redstonee/XClock/resource/Overview/IMG_20241222_154358.jpg

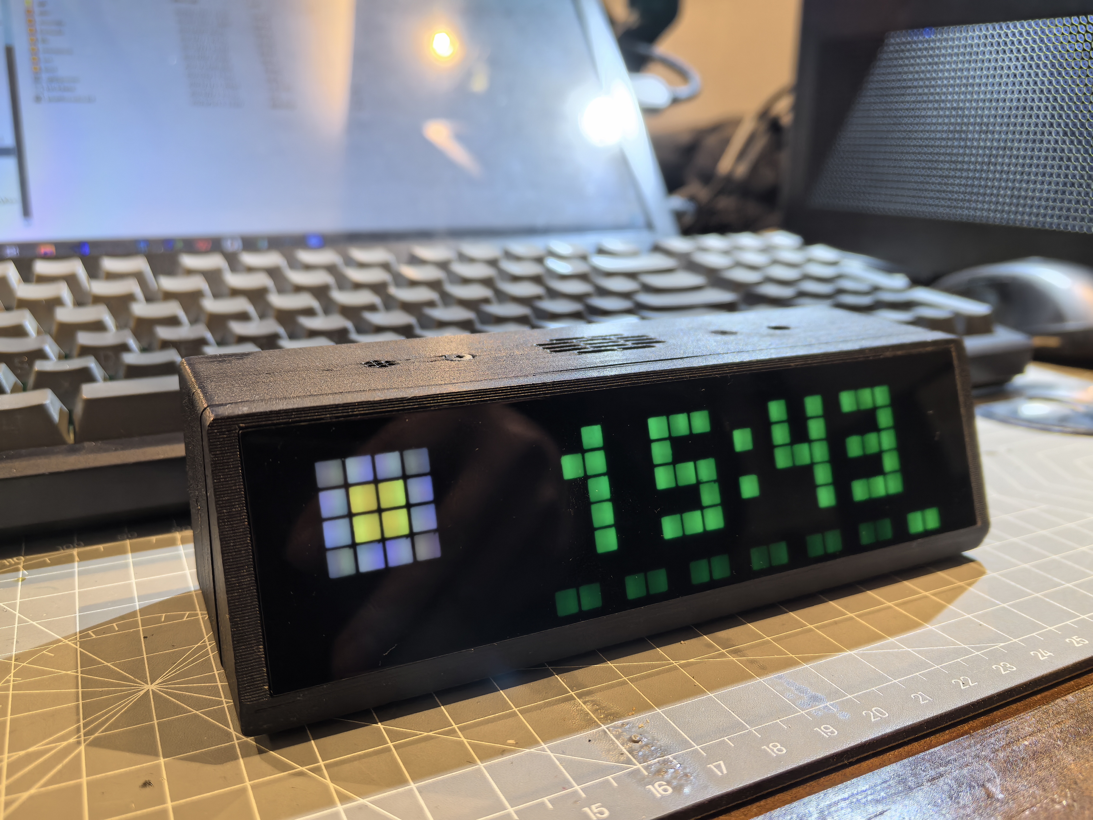
resource/Overview/IMG_20241222_154358.jpg
