redstonee/XClock/resource/Overview/IMG_20241222_154428.jpg

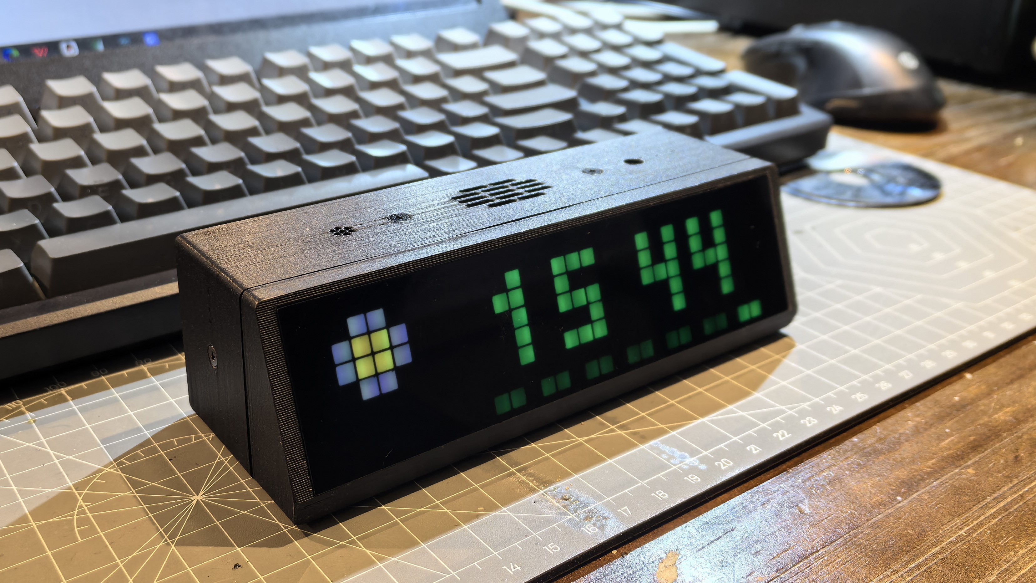
resource/Overview/IMG_20241222_154428.jpg
