redstonee/XClock/resource/Overview/IMG_20241222_154616.jpg

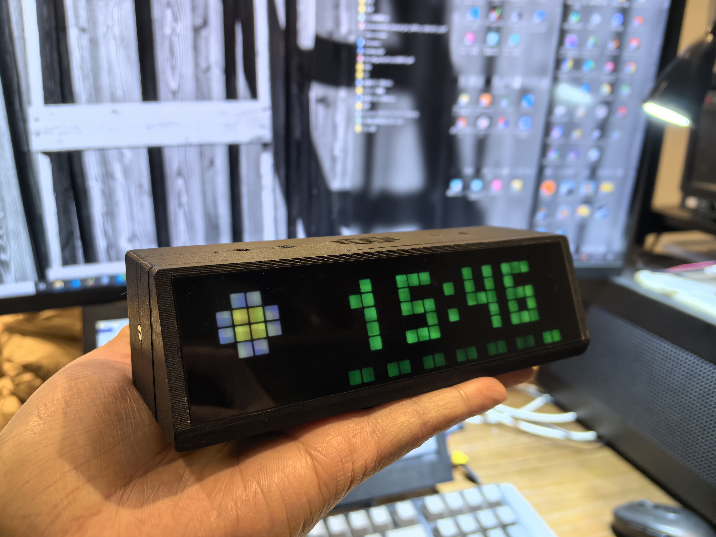
resource/Overview/IMG_20241222_154616.jpg
