redstonee/XClock/resource/Overview/IMG_20241222_154702.jpg

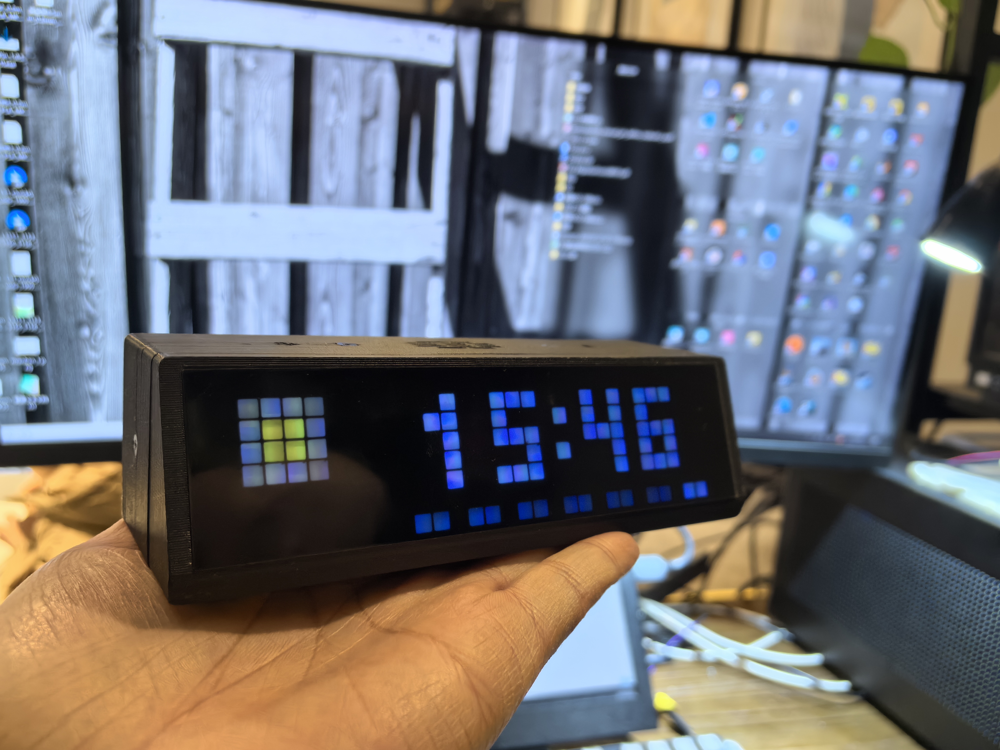
resource/Overview/IMG_20241222_154702.jpg
