redstonee/XClock/resource/Overview/IMG_20241222_154757.jpg

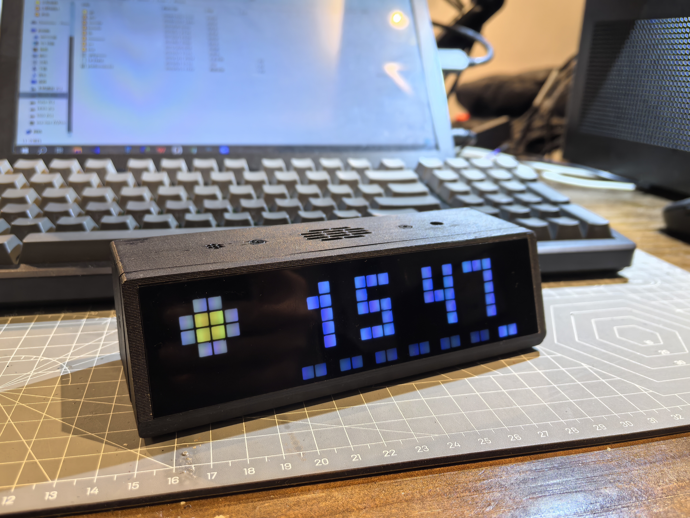
resource/Overview/IMG_20241222_154757.jpg
