redstonee/XClock/resource/Overview/IMG_20241222_154823.jpg

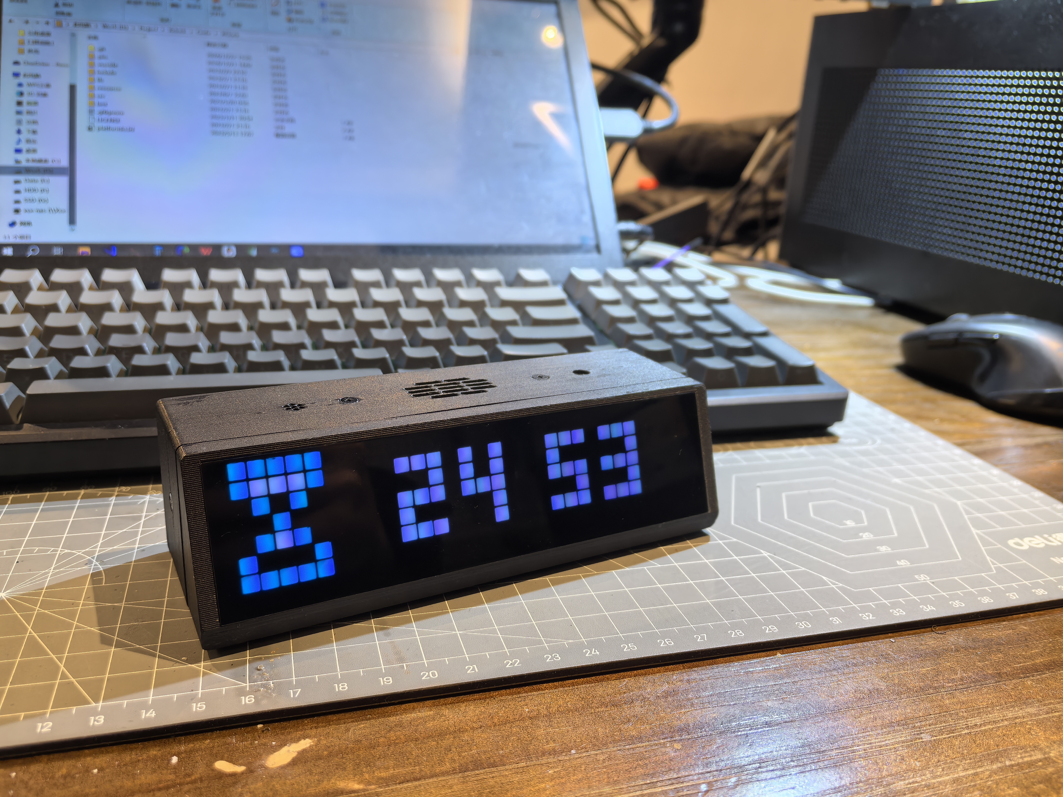
resource/Overview/IMG_20241222_154823.jpg
