redstonee/XClock/resource/Overview/IMG_20241222_154830.jpg

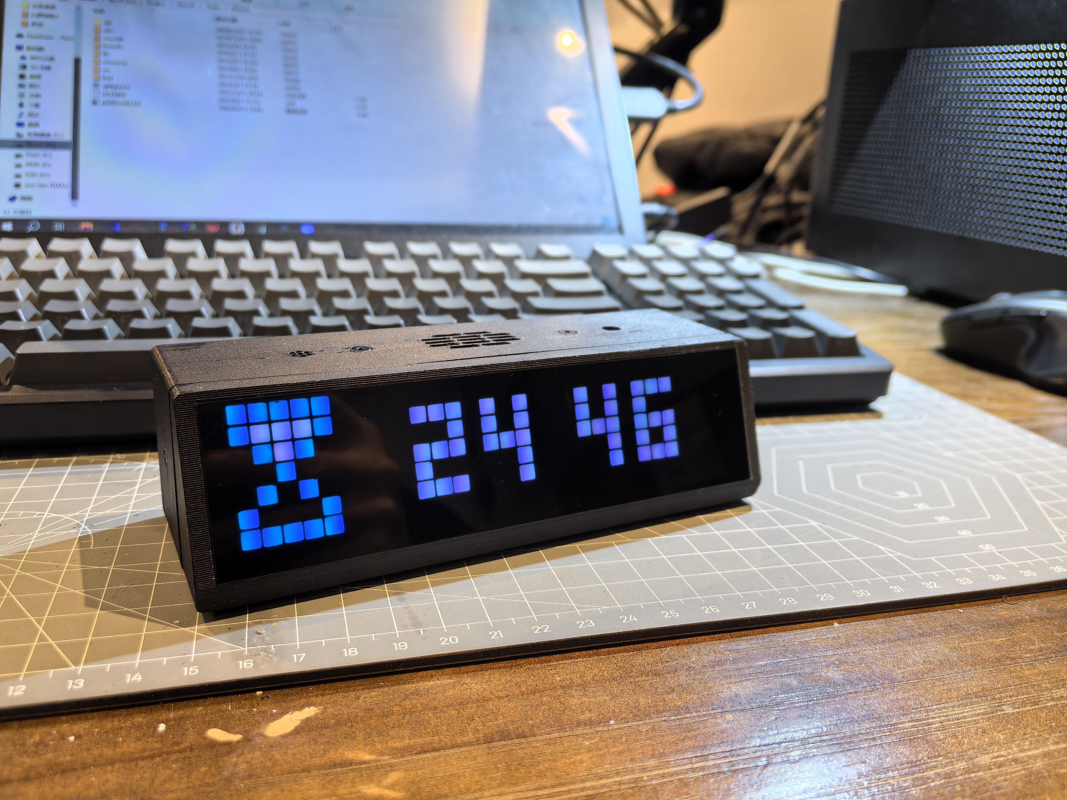
resource/Overview/IMG_20241222_154830.jpg
