redstonee/XClock/resource/Overview/IMG_20241222_155135.jpg

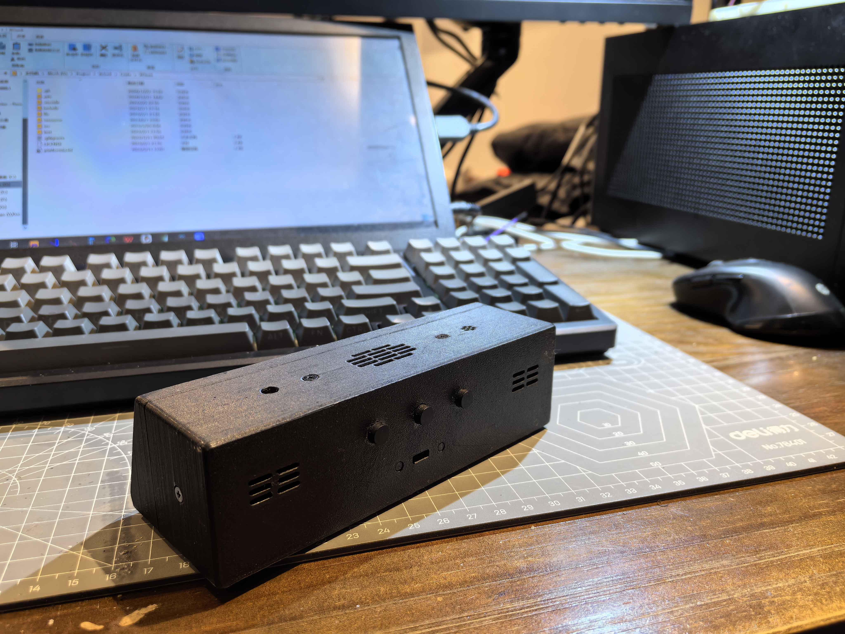
resource/Overview/IMG_20241222_155135.jpg
