redstonee/XClock/resource/Overview/IMG_20241222_163454.jpg

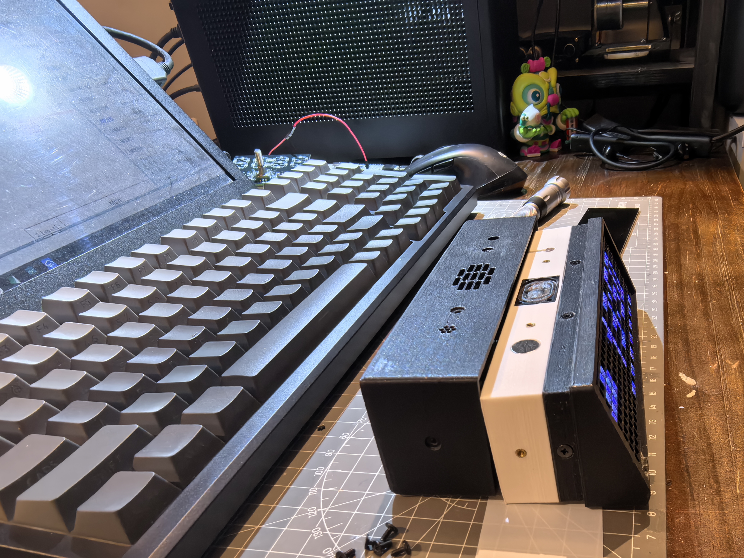
resource/Overview/IMG_20241222_163454.jpg
