redstonee/XClock/resource/Overview/IMG_20241222_1544281.jpg

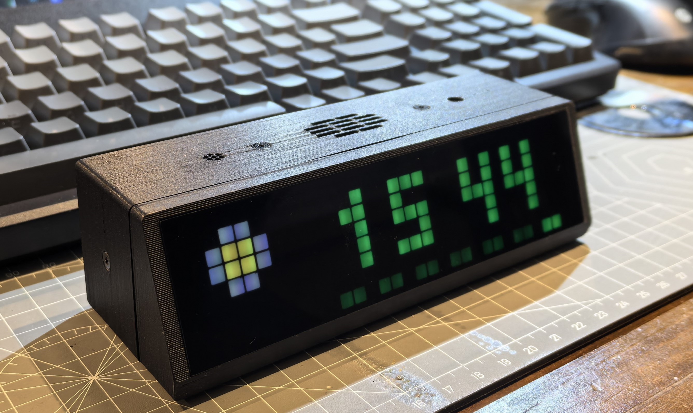
resource/Overview/IMG_20241222_1544281.jpg
