redstonee/XClock/resource/图标/GIF制作步骤/Pixilart画像素图片1.jpg

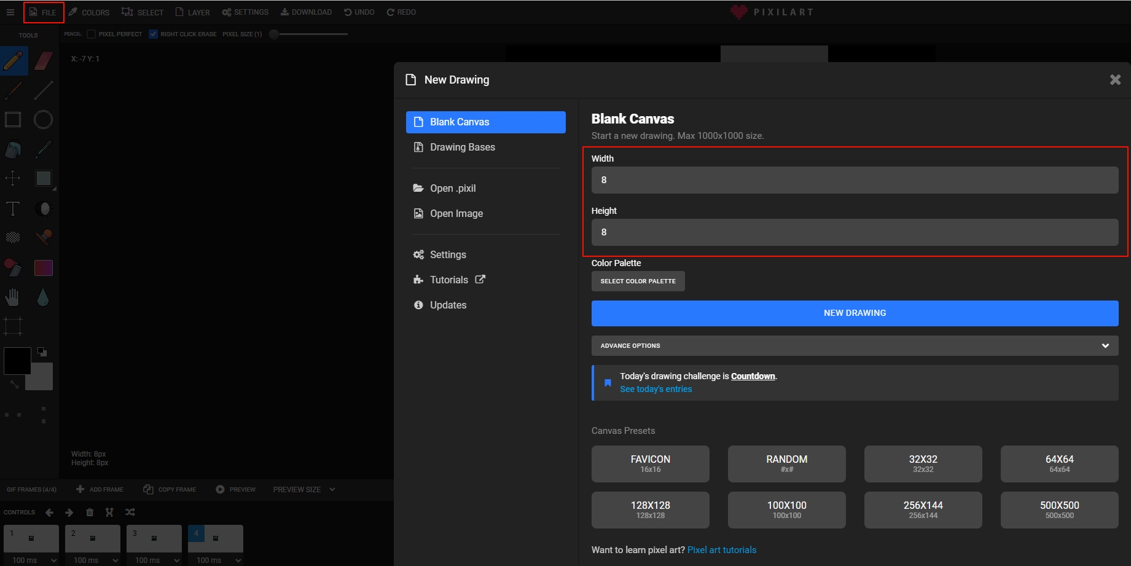
resource/图标/GIF制作步骤/Pixilart画像素图片1.jpg
