redstonee/XClock/resource/图标/GIF制作步骤/Pixilart画像素图片5.jpg

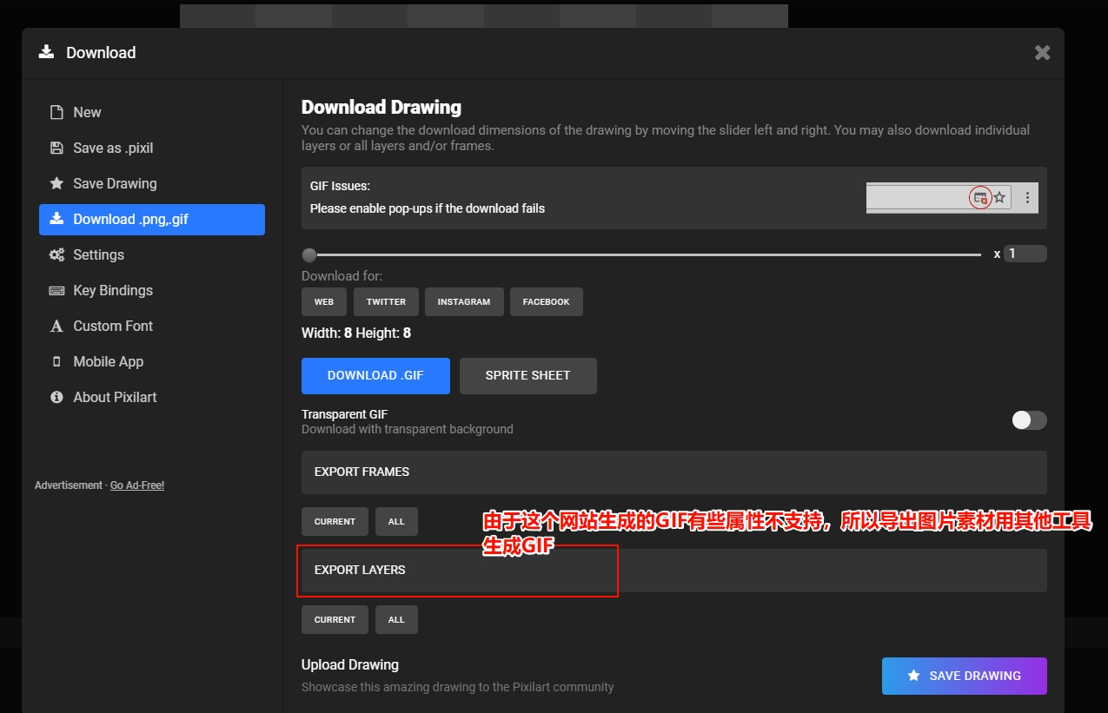
resource/图标/GIF制作步骤/Pixilart画像素图片5.jpg
