redstonee/XClock/resource/图标/GIF制作步骤/Step2.jpg

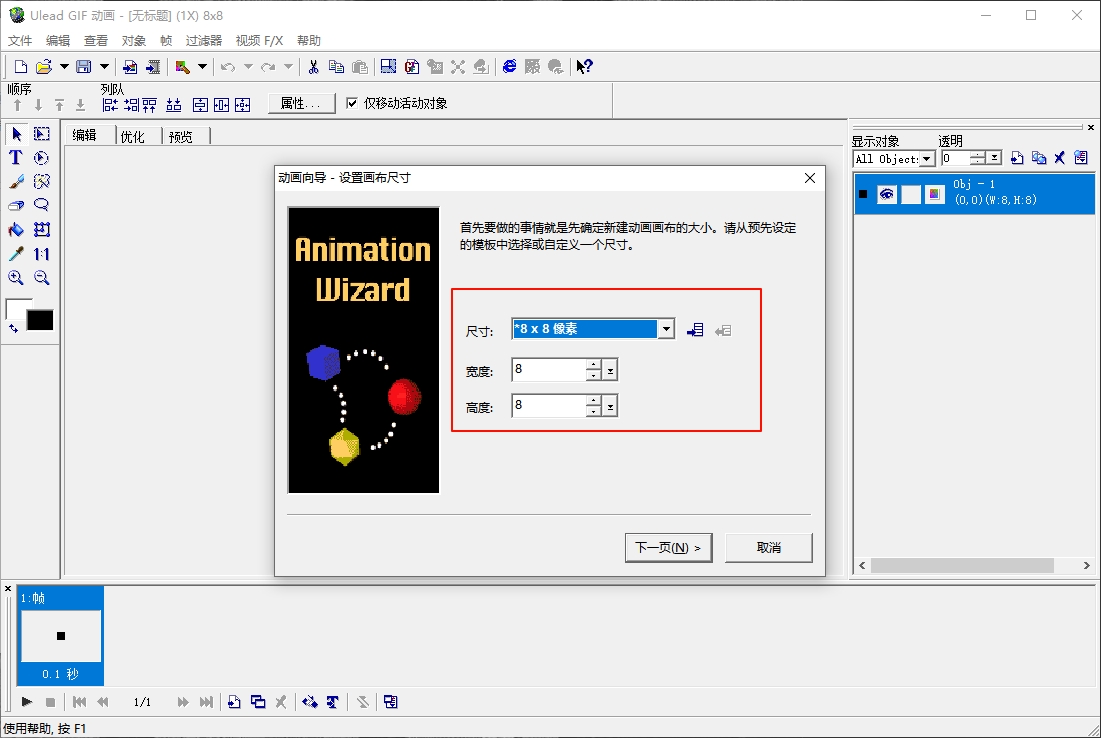
resource/图标/GIF制作步骤/Step2.jpg
