redstonee/XClock/resource/图标/GIF制作步骤/Step4.jpg

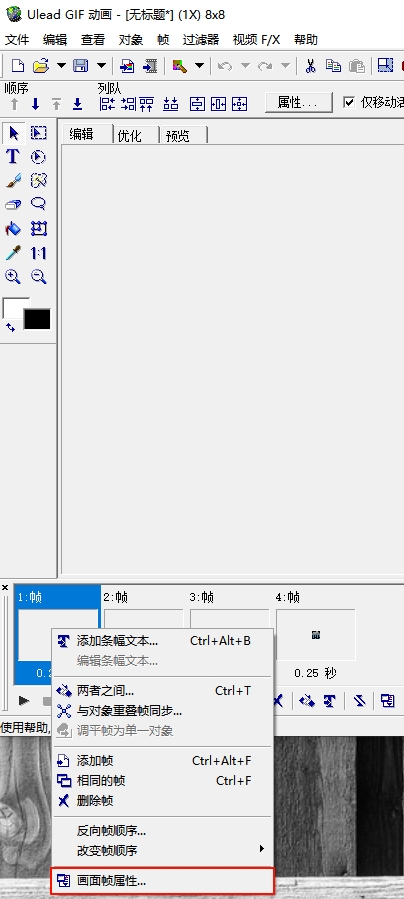
resource/图标/GIF制作步骤/Step4.jpg
