redstonee/XClock/src/Matrix/Palette.cpp

#include "Palette.h"
#include <Preferences.h>

#define MaxPaletteNum (sizeof(PaletteList) / sizeof(TProgmemRGBGradientPalette_bytes))
#define PrefKey_PaletteSpace "Palette"
#define PrefKey_PaletteIdx "PaletteIdx"
#define PrefKey_PaletteColIdx "PaletteColIdx"

// Gradient palette "GMT_sealand_gp", originally from
// http://soliton.vm.bytemark.co.uk/pub/cpt-city/gmt/tn/GMT_sealand.png.index.html
// converted for FastLED with gammas (2.6, 2.2, 2.5)
// Size: 80 bytes of program space.

static const char *TAG = "Palette";

DEFINE_GRADIENT_PALETTE(GMT_sealand_gp){
    0, 53, 33, 255,
    14, 23, 33, 255,
    28, 23, 68, 255,
    42, 23, 115, 255,
    56, 23, 178, 255,
    70, 23, 255, 255,
    84, 23, 255, 170,
    99, 23, 255, 103,
    113, 23, 255, 56,
    127, 23, 255, 25,
    141, 53, 255, 25,
    155, 100, 255, 25,
    170, 167, 255, 25,
    170, 255, 255, 87,
    184, 255, 193, 87,
    198, 255, 141, 87,
    212, 255, 99, 87,
    226, 255, 115, 135,
    240, 255, 135, 182,
    255, 255, 156, 223};

// Gradient palette "GMT_seafloor_gp", originally from
// http://soliton.vm.bytemark.co.uk/pub/cpt-city/gmt/tn/GMT_seafloor.png.index.html
// converted for FastLED with gammas (2.6, 2.2, 2.5)
// Size: 88 bytes of program space.

DEFINE_GRADIENT_PALETTE(GMT_seafloor_gp){
    0, 25, 0, 109,
    10, 28, 0, 119,
    21, 32, 0, 127,
    31, 35, 0, 140,
    42, 27, 1, 145,
    53, 20, 1, 151,
    74, 14, 4, 156,
    84, 9, 9, 164,
    95, 5, 15, 170,
    106, 2, 24, 176,
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
    127, 247, 248, 255,
    130, 247, 248, 255,
    130, 229, 233, 255,
    134, 229, 233, 255,
    134, 210, 217, 255,
    138, 210, 217, 255,
    138, 194, 203, 255,
    142, 194, 203, 255,
    142, 177, 187, 255,
    146, 177, 187, 255,
    146, 159, 171, 255,
    150, 159, 171, 255,
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

// Gradient palette "textbook_gp", originally from
// http://soliton.vm.bytemark.co.uk/pub/cpt-city/fme/metres/tn/textbook.png.index.html
// converted for FastLED with gammas (2.6, 2.2, 2.5)
// Size: 56 bytes of program space.

DEFINE_GRADIENT_PALETTE(textbook_gp){
    0, 5, 255, 6,
    8, 64, 255, 1,
    17, 135, 255, 0,
    25, 169, 193, 1,
    33, 210, 157, 2,
    42, 255, 125, 6,
    51, 255, 73, 21,
    59, 255, 53, 34,
    68, 184, 66, 67,
    76, 126, 81, 67,
    84, 82, 97, 106,
    93, 153, 166, 255,
    102, 199, 207, 255,
    255, 255, 255, 255};

// Gradient palette "autumnrose_gp", originally from
// http://soliton.vm.bytemark.co.uk/pub/cpt-city/rc/tn/autumnrose.png.index.html
// converted for FastLED with gammas (2.6, 2.2, 2.5)
// Size: 32 bytes of program space.

DEFINE_GRADIENT_PALETTE(autumnrose_gp){
    0, 71, 3, 1,
    45, 128, 5, 2,
    84, 186, 11, 3,
    127, 215, 27, 8,
    153, 224, 69, 13,
    188, 229, 84, 6,
    226, 242, 135, 17,
    255, 247, 161, 79};

TProgmemRGBGradientPalette_bytes PaletteList[] = {
    GMT_sealand_gp,
    GMT_seafloor_gp,
    rainbow_gp,
    bhw1_07_gp,
    bhw1_01_gp,
    bhw1_03_gp,
    bath_112_gp,
    seismic_gp,
    textbook_gp,
    autumnrose_gp};

uint8_t u8GetGlobalPaltIdx(void)
{
  uint8_t PaletteIdx = 0;
  Preferences pref;
  pref.begin(PrefKey_PaletteSpace);
  PaletteIdx = pref.getUChar(PrefKey_PaletteIdx, 0);
  pref.end();
  return PaletteIdx;
}

bool boSetGlobalPaltIdx(uint8_t idx)
{
  bool res = true;
  Preferences pref;
  pref.begin(PrefKey_PaletteSpace);
  if (idx < MaxPaletteNum)
  {
    pref.putUChar(PrefKey_PaletteIdx, idx);
    ESP_LOGI(TAG, "MaxPaletteNum1 %d", MaxPaletteNum);
  }
  else
  {
    ESP_LOGI(TAG, "MaxPaletteNum2 %d", MaxPaletteNum);
    res = false;
  }
  pref.end();
  return res;
}

uint8_t u8GetGlobalColorIdx(void)
{
  uint8_t ColorIdx = 0;
  Preferences pref;
  pref.begin(PrefKey_PaletteSpace);
  ColorIdx = pref.getUChar(PrefKey_PaletteColIdx, 0);
  pref.end();
  return ColorIdx;
}

bool boSetGlobalColorIdx(uint8_t idx)
{
  bool res = true;
  Preferences pref;
  pref.begin(PrefKey_PaletteSpace);
  pref.putUChar(PrefKey_PaletteColIdx, idx);
  pref.end();
  return res;
}

CRGBPalette16 pGetPalette(uint8_t Index)
{
  CRGBPalette16 Palette(PaletteList[Index]);
  return Palette;
}
