redstonee/XClock/src/Matrix/Icon.h

#ifndef __ICON_H__
#define __ICON_H__
/*Gif*/
const unsigned char icon_Sunny[] PROGMEM = {
	0x47, 0x49, 0x46, 0x38, 0x39, 0x61, 0x08, 0x00, 0x08, 0x00, 0xB2, 0x02, 0x00, 0x00, 0x00, 0x00, 
	0xFF, 0xFF, 0x00, 0x91, 0x91, 0x3F, 0x5E, 0x5E, 0x2B, 0x00, 0x00, 0x00, 0x00, 0x00, 0x00, 0x00, 
	0x00, 0x00, 0x00, 0x00, 0x00, 0x21, 0xFF, 0x0B, 0x4E, 0x45, 0x54, 0x53, 0x43, 0x41, 0x50, 0x45, 
	0x32, 0x2E, 0x30, 0x03, 0x01, 0x00, 0x00, 0x00, 0x21, 0xF9, 0x04, 0x05, 0x28, 0x00, 0x04, 0x00, 
	0x2C, 0x00, 0x00, 0x00, 0x00, 0x08, 0x00, 0x08, 0x00, 0x00, 0x03, 0x0A, 0x08, 0xBA, 0xDC, 0x1C, 
	0xC1, 0x41, 0x47, 0xAB, 0x6D, 0x09, 0x00, 0x21, 0xF9, 0x04, 0x05, 0x28, 0x00, 0x04, 0x00, 0x2C, 
	0x00, 0x00, 0x00, 0x00, 0x08, 0x00, 0x08, 0x00, 0x00, 0x03, 0x0E, 0x08, 0xBA, 0x0C, 0x22, 0x4D, 
	0x84, 0x00, 0x97, 0xA4, 0xB1, 0xB6, 0xCD, 0x79, 0x02, 0x00, 0x21, 0xF9, 0x04, 0x05, 0x28, 0x00, 
	0x04, 0x00, 0x2C, 0x00, 0x00, 0x00, 0x00, 0x08, 0x00, 0x08, 0x00, 0x00, 0x03, 0x10, 0x08, 0xBA, 
	0x3C, 0x22, 0x83, 0x89, 0x10, 0x84, 0xA4, 0x76, 0x39, 0xC8, 0xBA, 0xFF, 0x4C, 0x02, 0x00, 0x3B
};
/*Gif*/
const unsigned char icon_Clear[] PROGMEM = {
	0x47, 0x49, 0x46, 0x38, 0x39, 0x61, 0x08, 0x00, 0x08, 0x00, 0xB2, 0x01, 0x00, 0x00, 0x00, 0x00, 
	0xBA, 0xBA, 0x30, 0x5E, 0x5E, 0x2B, 0xFF, 0xFF, 0x00, 0x3B, 0x3B, 0x09, 0x00, 0x00, 0x00, 0x00, 
	0x00, 0x00, 0x00, 0x00, 0x00, 0x21, 0xF9, 0x04, 0x04, 0x0A, 0x00, 0xFF, 0x00, 0x2C, 0x00, 0x00, 
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
	0x00, 0xFF, 0x00, 0x00, 0x00, 0x00, 0x00, 0x00, 0xFF, 0xFF, 0xFF, 0x00, 0x00, 0x00, 0x00, 0x00, 
	0x00, 0x00, 0x00, 0x00, 0xFF, 0xFF, 0xFF, 0xFF, 0xFF, 0xFF, 0xFF, 0xFF, 0xFF, 0xFF, 0xFF, 0xFF, 
	0x00, 0x00, 0x00, 0x00, 0x00, 0x00
};

#endif //__ICON_H__
