redstonee/XClock/src/Matrix/FFT.h

/****************************************************************************
Copyright (c) 2021      Yinbaiyuan

https://www.yinbaiyuan.com

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
THE SOFTWARE IS PROVIDED "AS IS", WITHOUT WARRANTY OF ANY KIND, EXPRESS OR
IMPLIED, INCLUDING BUT NOT LIMITED TO THE WARRANTIES OF MERCHANTABILITY,
FITNESS FOR A PARTICULAR PURPOSE AND NONINFRINGEMENT. IN NO EVENT SHALL THE
AUTHORS OR COPYRIGHT HOLDERS BE LIABLE FOR ANY CLAIM, DAMAGES OR OTHER
LIABILITY, WHETHER IN AN ACTION OF CONTRACT, TORT OR OTHERWISE, ARISING FROM,
OUT OF OR IN CONNECTION WITH THE SOFTWARE OR THE USE OR OTHER DEALINGS IN
THE SOFTWARE.
****************************************************************************/

#ifndef __FFT_H__
#define __FFT_H__

#include "Dot2D/dot2d.h"
#include <arduinoFFT.h>

#define SAMPLING_FREQ 8000
#define SAMPLES       64
#define FREQUENCY_BANDS 24
#define CONTENT_HIGHT   8
#define CONTENT_WIDTH   32
NS_DT_BEGIN

class FFT : public Scene
{

protected:

    bool init() override;

public:

    STATIC_CREATE(FFT);

};

class FFTLayer : public Layer
{
protected:
    
    uint8_t animateCount = 0;
    double hzPerSample = SAMPLING_FREQ / SAMPLES;
    double realComponent[64];
    double imagComponent[64];
    double coutoffFrequencies[FREQUENCY_BANDS];
    double maxinband[FREQUENCY_BANDS];
    double median_pre[FREQUENCY_BANDS];
    float reference;
    arduinoFFT* fft;

public:

    virtual ~FFTLayer();

protected:
    
    CanvasSprite* canvasSprite = nullptr;
    FrameSprite* music_icon = nullptr;
public:

    STATIC_CREATE(FFTLayer);

    virtual bool initLayer();
    
    void update(float dt) override;

};

/*Music icon, GIF*/
const unsigned char icon_music[] PROGMEM  = {
	0x47, 0x49, 0x46, 0x38, 0x39, 0x61, 0x08, 0x00, 0x08, 0x00, 0xF6, 0x02, 0x00, 0x00, 0x00, 0x00, 
	0xF4, 0x8F, 0xB1, 0xF8, 0xBB, 0xD0, 0xFF, 0x80, 0xAB, 0xF0, 0x62, 0x92, 0xFF, 0x40, 0x81, 0xF5, 
	0x00, 0x57, 0xC5, 0x11, 0x62, 0xAB, 0x47, 0xBC, 0xBA, 0x68, 0xC8, 0x9C, 0x27, 0xB0, 0x8E, 0x24, 
	0xAA, 0x7B, 0x1F, 0xA2, 0x6A, 0x1B, 0x9A, 0x4A, 0x14, 0x8C, 0x7E, 0x57, 0xC2, 0x95, 0x75, 0xCD, 
	0x67, 0x3A, 0xB7, 0x5E, 0x35, 0xB1, 0x51, 0x2D, 0xA8, 0x45, 0x27, 0xA0, 0x31, 0x1B, 0x92, 0x5C, 
	0x6B, 0xC0, 0x79, 0x86, 0xCB, 0x3F, 0x51, 0xB5, 0x39, 0x49, 0xAB, 0x30, 0x3F, 0x9F, 0x28, 0x35, 
	0x93, 0x1A, 0x23, 0x7E, 0x42, 0xA5, 0xF5, 0x64, 0xB5, 0xF6, 0x21, 0x96, 0xF3, 0x1E, 0x88, 0xE5, 
	0x19, 0x76, 0xD2, 0x15, 0x65, 0xC0, 0x0D, 0x47, 0xA1, 0x29, 0xB6, 0xF6, 0x4F, 0xC3, 0xF7, 0x03, 
	0xA9, 0xF4, 0x03, 0x9B, 0xE5, 0x02, 0x88, 0xD1, 0x02, 0x77, 0xBD, 0x01, 0x57, 0x9B, 0x26, 0xC6, 
	0xDA, 0x4D, 0xD0, 0xE1, 0x00, 0xBC, 0xD4, 0x00, 0xAC, 0xC1, 0x00, 0x97, 0xA7, 0x00, 0x83, 0x8F, 
	0x00, 0x60, 0x64, 0x26, 0xA6, 0x9A, 0x4D, 0xB6, 0xAC, 0x00, 0x96, 0x88, 0x00, 0x89, 0x7B, 0x00, 
	0x79, 0x6B, 0x00, 0x69, 0x5C, 0x00, 0x4D, 0x40, 0x66, 0xBB, 0x6A, 0x81, 0xC7, 0x84, 0x4C, 0xAF, 
	0x50, 0x43, 0xA0, 0x47, 0x38, 0x8E, 0x3C, 0x2E, 0x7D, 0x32, 0x1B, 0x5E, 0x20, 0xD4, 0xE1, 0x57, 
	0xDC, 0xE7, 0x75, 0xCD, 0xDC, 0x39, 0xC0, 0xCA, 0x33, 0xAF, 0xB4, 0x2B, 0x9E, 0x9D, 0x24, 0x82, 
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
	0x83, 0x84, 0x82, 0x16, 0x17, 0x88, 0x84, 0x18, 0x86, 0x84, 0x19, 0x82, 0x8B, 0x82, 0x1A, 0x1A, 
	0x82, 0x8E, 0x00, 0x1B, 0x96, 0x00, 0x92, 0x83, 0x1C, 0x98, 0x97, 0x85, 0x9C, 0x81, 0x00, 0x21, 
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
};

NS_DT_END

#endif //__FFT_H__
