redstonee/XClock/src/Matrix/TimerScene.cpp

#include "TimerScene.h"
#include "Dot2D/third/gfxfont.h"
#include "Dot2D/third/Picopixel.h"
#include "Dot2D/third/TomThumb.h"
#include "FastLED.h"
#include "Icon.h"
#include "ClockKey.h"

NS_DT_BEGIN

typedef struct
{
    uint8_t u8MSec;
    uint8_t minute;
    uint8_t second;
    bool boTiming;
}tstTimerType;

tstTimerType GlobalTimer = {0,0,0,false};
TimerHandle_t TimerCounter = nullptr;
/********************************Timer sence and layer****************************************/

bool boIsTimerCounterActive()
{
    bool boRes = false;
    if(nullptr != TimerCounter)
    {
        boRes = xTimerIsTimerActive(TimerCounter);
    }
    return boRes;
}

void TimerCounterCb(TimerHandle_t xTimer)
{
    if(++GlobalTimer.u8MSec >= 100)
    {
        GlobalTimer.u8MSec = 0;
        if(++GlobalTimer.second >= 60)
        {
            GlobalTimer.second = 0;
            if(++GlobalTimer.minute >= 100)
            {
                GlobalTimer.minute = 99;
                GlobalTimer.second = 99;
                GlobalTimer.u8MSec = 99;
                xTimerStop(TimerCounter,10);
            }
        }
    }
}

bool TimerScene::init()
{
    TimerLayer *Timerlayer = TimerLayer::create();
    Timerlayer->setContentSize(Size(32,8));
    Timerlayer->setPosition(0,0);
    //ClockLayer->setOpacity
    this->addChild(Timerlayer);
    Timerlayer->initLayer();
    
    return true;
}

bool TimerLayer::initLayer()
{
    auto listener = EventListenerButton::create();
    listener ->onBtnDuringLongPress = DT_CALLBACK_2(TimerLayer::BtnDuringLongPressHandler,this);
    listener ->onBtnLongPressStart = DT_CALLBACK_2(TimerLayer::BtnLongPressStartHandler,this);
    listener ->onBtnClick = DT_CALLBACK_2(TimerLayer::BtnClickHandler,this);   
    listener ->onBtnDoubleClick = DT_CALLBACK_2(TimerLayer::BtnDoubleClickHandler,this);  
    _eventDispatcher->addEventListenerWithSceneGraphPriority ( listener, this );
    if(false == GlobalTimer.boTiming)
    {
        GlobalTimer.u8MSec = 0;
        GlobalTimer.minute = 0;
        GlobalTimer.second = 0;
    }
    DTRGB TextColor = {255,255,255};
    MSec = TextSprite::create(Size(8,5),Size(8,5),TextColor,(std::to_string(GlobalTimer.u8MSec/10)+std::to_string(GlobalTimer.u8MSec%10)),TextSprite::TextAlign::TextAlignRight,&TomThumb);
    MSeccanvas = MSec->getSpriteCanvas();
    TimePt1 = TextSprite::create(Size(2,5),Size(2,5),TextColor,":",TextSprite::TextAlign::TextAlignCenter,&TomThumb);
    TimePt1canvas = TimePt1->getSpriteCanvas();
    Min = TextSprite::create(Size(8,5),Size(8,5),TextColor,(std::to_string(GlobalTimer.minute/10) + std::to_string(GlobalTimer.minute%10)),TextSprite::TextAlign::TextAlignRight,&TomThumb);
    Mincanvas = Min->getSpriteCanvas();
    TimePt2 = TextSprite::create(Size(2,5),Size(2,5),TextColor,".",TextSprite::TextAlign::TextAlignCenter,&TomThumb);
    TimePt2canvas = TimePt2->getSpriteCanvas();
    Sec = TextSprite::create(Size(8,5),Size(8,5),TextColor,(std::to_string(GlobalTimer.second/10) + std::to_string(GlobalTimer.second%10)),TextSprite::TextAlign::TextAlignRight,&TomThumb);
    Seccanvas = Sec->getSpriteCanvas();
    MSec->setPosition(23,1);
    TimePt1->setPosition(11,1);
    Min->setPosition(3,1);
    TimePt2->setPosition(21,1);    
    Sec->setPosition(13,1);
    this->addChild(MSec);
    this->addChild(TimePt1);
    this->addChild(Min);
    this->addChild(TimePt2);
    this->addChild(Sec);
    this->scheduleUpdate();
    this->schedule(DT_SCHEDULE_SELECTOR(TimerLayer::TimerUpdate),0.03);
    if(nullptr == TimerCounter)
    {
        TimerCounter = xTimerCreate
                   ( /* Just a text name, not used by the RTOS
                     kernel. */
                     "FeatureTimer",
                     /* The timer period in ticks, must be
                     greater than 0. */
                     (portTICK_PERIOD_MS*10),
                     /* The timers will auto-reload themselves
                     when they expire. */
                     pdTRUE,
                     /* The ID is used to store a count of the
                     number of times the timer has expired, which
                     is initialised to 0. */
                     ( void * ) 0,
                     /* Each timer calls the same callback when
                     it expires. */
                     TimerCounterCb
                   );
    }
    
    return true;
}



void TimerLayer::TimerUpdate(float dt)
{
    static tstTimerType TimerPre = GlobalTimer;
    if(GlobalTimer.boTiming)
    {
        if(0 == TimePt1->getNumberOfRunningActions())
        {
            TimePt1->runAction(RepeatForever::create(Blink::create(1,1)));
        }        
    }
    else
    {
        if(0 != TimePt1->getNumberOfRunningActions())
        {
            TimePt1->stopAllActions();
            TimePt1->setVisible(true);
        }        
    }
    if(TimerPre.u8MSec != GlobalTimer.u8MSec)
    {
        MSeccanvas->canvasReset();
        MSeccanvas->print((std::to_string(GlobalTimer.u8MSec/10)+std::to_string(GlobalTimer.u8MSec%10)).c_str());
    }
    if(TimerPre.minute != GlobalTimer.minute)
    {
        Mincanvas->canvasReset();
        Mincanvas->print((std::to_string(GlobalTimer.minute/10) + std::to_string(GlobalTimer.minute%10)).c_str());
    }
    if(TimerPre.second != GlobalTimer.second)
    {
        Seccanvas->canvasReset();
        Seccanvas->print((std::to_string(GlobalTimer.second/10) + std::to_string(GlobalTimer.second%10)).c_str());
    }
    TimerPre = GlobalTimer;
}

void TimerLayer::BtnClickHandler(int8_t keyCode, Event* event)
{
    if(enKey_OK == keyCode)
    {   
        if(xTimerIsTimerActive(TimerCounter))
        {
            xTimerStop(TimerCounter,10);
            GlobalTimer.boTiming = false;
        }
        else
        {
            xTimerStart(TimerCounter,10);
            GlobalTimer.boTiming = true;
        }
    }
}

void TimerLayer::BtnDoubleClickHandler(int8_t keyCode, Event* event)
{

}

void TimerLayer::BtnLongPressStartHandler(int8_t keyCode, Event* event)
{
    if(enKey_OK == keyCode)
    {   
        if(xTimerIsTimerActive(TimerCounter))
        {
            xTimerStop(TimerCounter,10);
        }
        GlobalTimer.boTiming = false;
        GlobalTimer.u8MSec = 0;
        GlobalTimer.minute = 0;
        GlobalTimer.second = 0;
    }
}

void TimerLayer::BtnDuringLongPressHandler(int8_t keyCode, Event* event)
{

}


NS_DT_END
