redstonee/XClock/src/Matrix/CountDownTimer.h

#ifndef __COUNTDOWN_H__
#define __COUNTDOWN_H__
#include <Arduino.h>
#include "Dot2D/dot2d.h"

NS_DT_BEGIN

typedef enum
{
	Timer_Dis = 0,
	Timer_MinSetting,
	Timer_SecSetting
} tenTimerStatus;

#define CountDownTimerExit_TO (1000 * 60 * 10)

class CountDownScene : public Scene
{

protected:
	bool init() override;

public:
	STATIC_CREATE(CountDownScene);
};

class CountDownLayer : public Layer
{
private:
	uint8_t initialMinute, initialSecond;
	enum class TimerStatus
	{
		READY,
		COUNTING,
		FINISHED
	};

	struct CountTimer
	{
		uint8_t minute;
		uint8_t second;
		TimerStatus status;
	};

	CountTimer countTimerConfig = {0, 0, TimerStatus::READY};
	TimerHandle_t counterTimer = nullptr;
	TimerHandle_t inactiveTimer = nullptr;
	static bool isActive;

	static void ExitTimerCb(TimerHandle_t xTimer);
	static void CounterTimerCb(TimerHandle_t xTimer);

protected:
	FrameSprite *TimerIcon = nullptr;
	TextSprite *Min = nullptr;
	SpriteCanvas *Mincanvas = nullptr;
	TextSprite *TimePt = nullptr;
	SpriteCanvas *TimePtcanvas = nullptr;
	TextSprite *Sec = nullptr;
	SpriteCanvas *Seccanvas = nullptr;
	tenTimerStatus enTimerSts = Timer_Dis;

public:
	STATIC_CREATE(CountDownLayer);

	virtual bool initLayer();

	void TimerUpdate(float dt);

	void TimerMachine(int8_t, int8_t);

	void BtnClickHandler(int8_t, Event *);

	void BtnDoubleClickHandler(int8_t, Event *);

	void BtnLongPressStartHandler(int8_t, Event *);

	void BtnDuringLongPressHandler(int8_t, Event *);
	
	static bool isCountDownTimerActive();
};

/*************icon of active timer,gif*************/

const unsigned char icon_TimerActive[] PROGMEM = {
	0x47, 0x49, 0x46, 0x38, 0x39, 0x61, 0x08, 0x00, 0x08, 0x00, 0xA1, 0x02, 0x00, 0x00, 0x00, 0x00,
	0x00, 0xBB, 0xFF, 0xFF, 0xFF, 0xFF, 0x00, 0x00, 0x00, 0x21, 0xFF, 0x0B, 0x4E, 0x45, 0x54, 0x53,
	0x43, 0x41, 0x50, 0x45, 0x32, 0x2E, 0x30, 0x03, 0x01, 0x00, 0x00, 0x00, 0x21, 0xF9, 0x04, 0x05,
	0x28, 0x00, 0x03, 0x00, 0x2C, 0x00, 0x00, 0x00, 0x00, 0x08, 0x00, 0x08, 0x00, 0x00, 0x02, 0x0F,
	0x84, 0x8F, 0xA1, 0x7A, 0x21, 0x1F, 0x92, 0x88, 0x08, 0xD0, 0x64, 0xB1, 0xB9, 0x8B, 0x15, 0x00,
	0x21, 0xF9, 0x04, 0x05, 0x28, 0x00, 0x03, 0x00, 0x2C, 0x00, 0x00, 0x00, 0x00, 0x08, 0x00, 0x08,
	0x00, 0x00, 0x02, 0x10, 0x84, 0x8F, 0xA1, 0x7A, 0x21, 0x1F, 0x12, 0x88, 0x68, 0xD6, 0x29, 0xA8,
	0xD1, 0x7C, 0xC5, 0x02, 0x00, 0x21, 0xF9, 0x04, 0x05, 0x28, 0x00, 0x03, 0x00, 0x2C, 0x00, 0x00,
	0x00, 0x00, 0x08, 0x00, 0x08, 0x00, 0x00, 0x02, 0x11, 0x84, 0x8F, 0xA1, 0x7A, 0x21, 0x20, 0x42,
	0x8A, 0xC8, 0xC8, 0x2A, 0xAF, 0x85, 0x40, 0x2F, 0x56, 0x00, 0x00, 0x21, 0xF9, 0x04, 0x05, 0x28,
	0x00, 0x03, 0x00, 0x2C, 0x00, 0x00, 0x00, 0x00, 0x08, 0x00, 0x08, 0x00, 0x00, 0x02, 0x11, 0x84,
	0x8F, 0xA1, 0x7A, 0x21, 0x20, 0x42, 0x02, 0x12, 0x51, 0x4B, 0xE3, 0x7C, 0x95, 0x2E, 0x59, 0x00,
	0x00, 0x21, 0xF9, 0x04, 0x05, 0x28, 0x00, 0x03, 0x00, 0x2C, 0x00, 0x00, 0x00, 0x00, 0x08, 0x00,
	0x08, 0x00, 0x00, 0x02, 0x0F, 0x84, 0x8F, 0xA1, 0x7A, 0x21, 0x16, 0x92, 0x88, 0x08, 0xD0, 0x64,
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
	0xBB, 0x00, 0xFF, 0xBB, 0x00, 0xFF, 0xBB, 0x00, 0xFF, 0xBB, 0x00, 0x00, 0x00, 0x00, 0x00, 0x00,
	0x00, 0x00, 0x00, 0x00, 0x00, 0x00, 0x00, 0x00, 0x00, 0x00, 0x00, 0x00, 0x00, 0x00, 0x00, 0x00,
	0x00, 0x00, 0x00, 0x00, 0x00, 0x00};

NS_DT_END

#endif //__COUNTDOWN_H__
